royrobotiks/card10_cover/stls/WristbandParts/MClip.stl

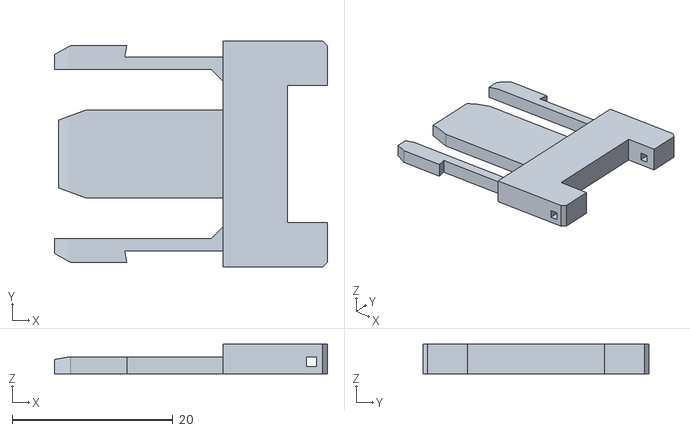
[picture p25: CAD file, 2019-10-05]
stls/WristbandParts/MClip.stl
34.0 x 28.2 x 3.70
