royrobotiks/card10_cover/stls/WristbandParts/190mm_heartbeat.stl

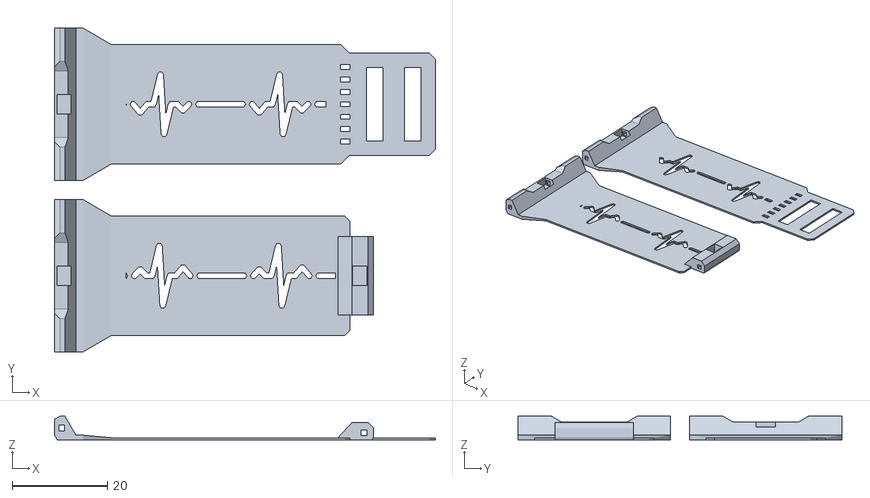
[picture p26: CAD file, 2019-10-05]
stls/WristbandParts/190mm_heartbeat.stl
80.0 x 68.0 x 5.00
