royrobotiks/card10_cover/stls/WristbandParts/FClip.stl

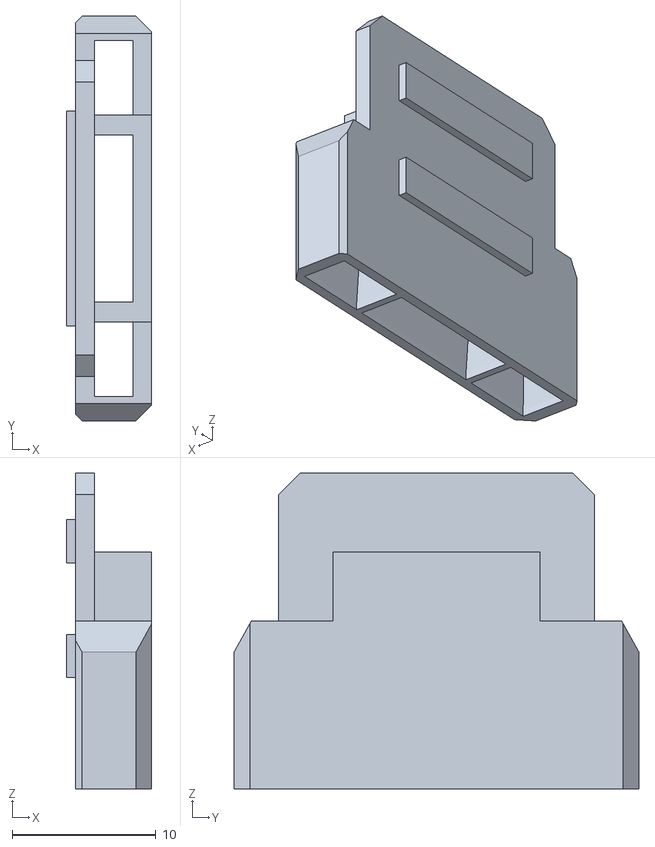
[picture p27: CAD file, 2019-10-05]
stls/WristbandParts/FClip.stl
5.95 x 28.2 x 22.0
